jjsprandel/SCAN_PCB/hardware_design/exports/3d_models/full_back_zoomed.png

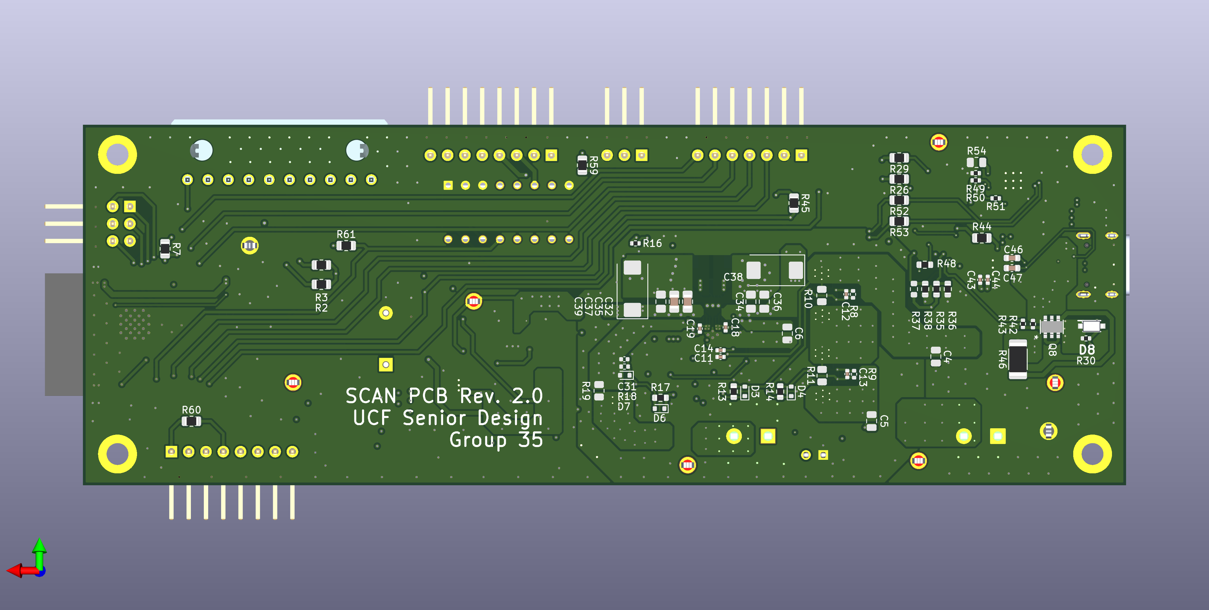
hardware_design/exports/3d_models/full_back_zoomed.png
