jjsprandel/SCAN_PCB/hardware_design/exports/3d_models/power_management.png

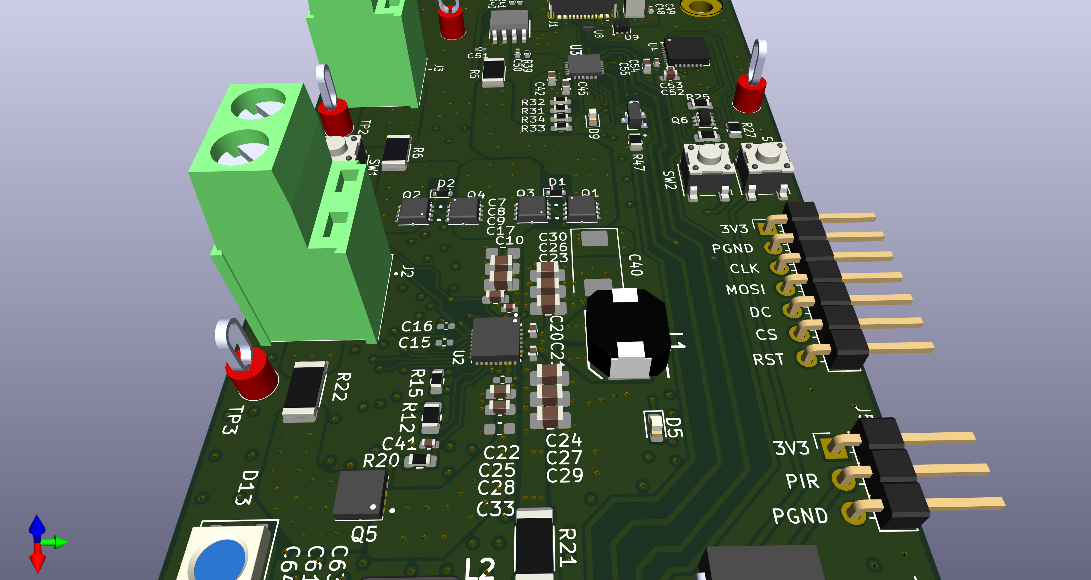
hardware_design/exports/3d_models/power_management.png
