jjsprandel/SCAN_PCB/hardware_design/exports/3d_models/regulators.png

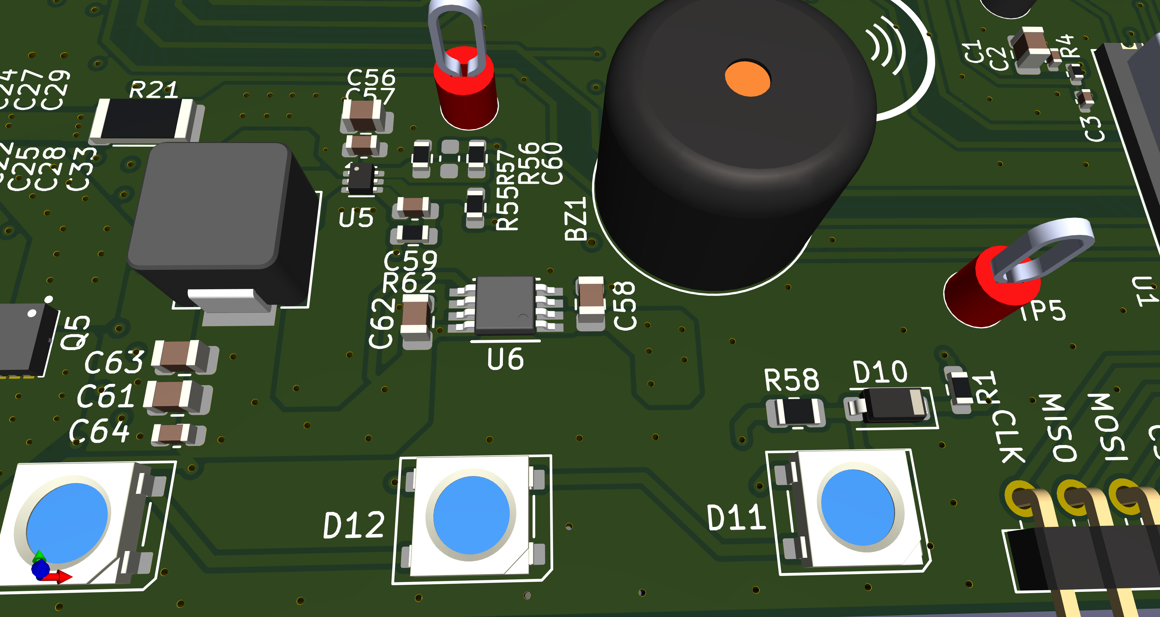
hardware_design/exports/3d_models/regulators.png
