jjsprandel/SCAN_PCB/hardware_design/exports/3d_models/side_1.png

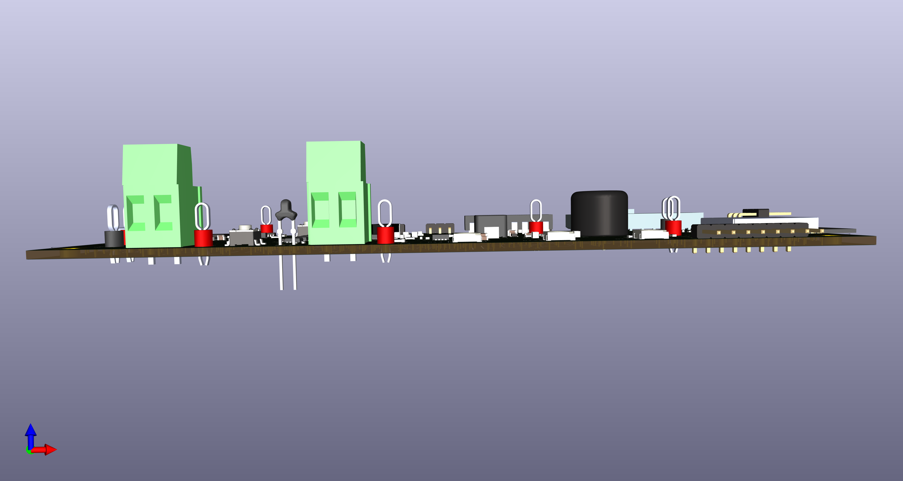
hardware_design/exports/3d_models/side_1.png
