jjsprandel/SCAN_PCB/hardware_design/exports/3d_models/USB_PD.png

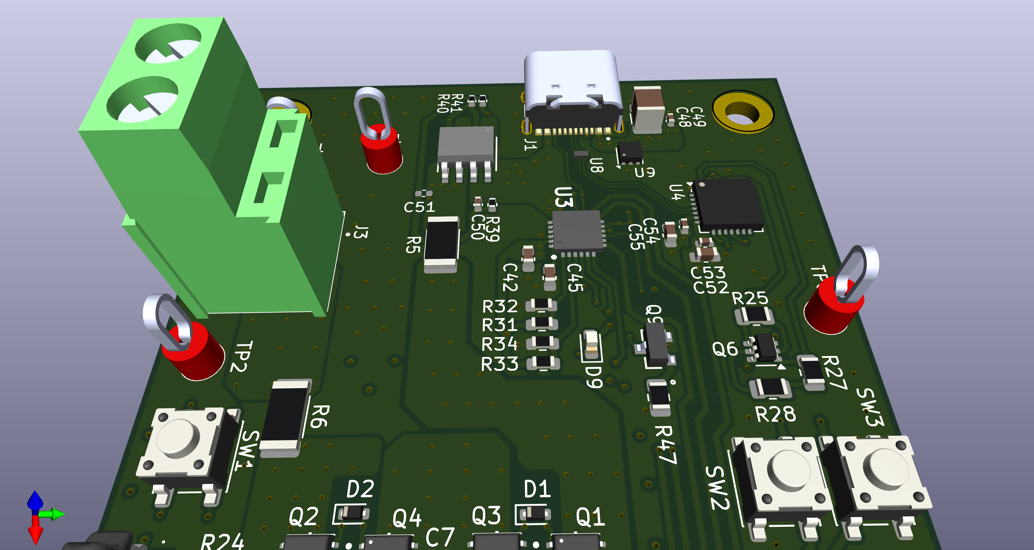
hardware_design/exports/3d_models/USB_PD.png
