jjsprandel/SCAN_PCB/hardware_design/exports/layout/multi-layer/top_gnd1.pdf

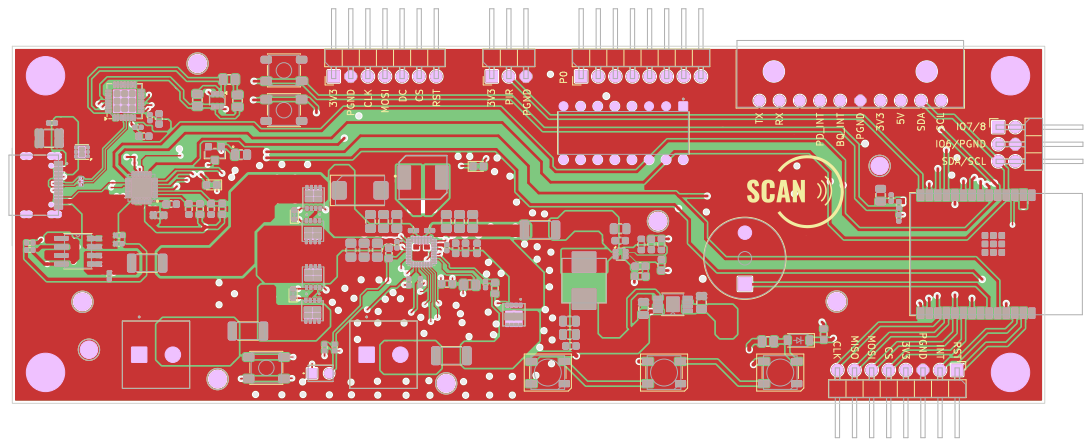
[picture p36: page 1]
