jjsprandel/SCAN_PCB/hardware_design/exports/layout/single_layer/SCAN-B_Adhesive.pdf

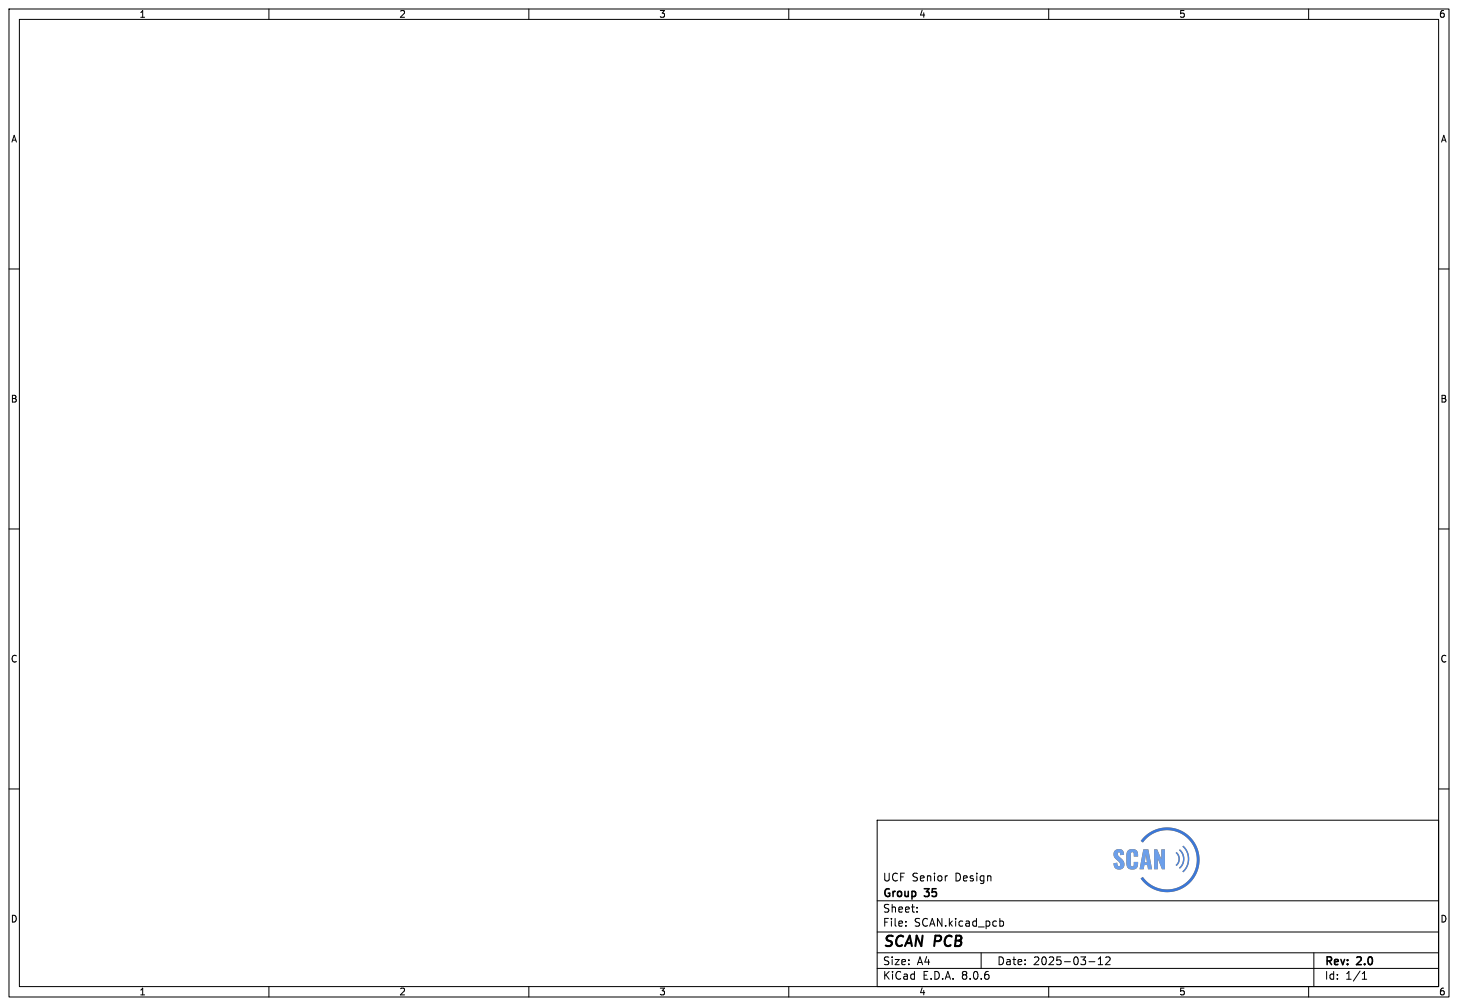
[picture p37: page 1]
