jjsprandel/SCAN_PCB/hardware_design/exports/layout/single_layer/SCAN-B_Courtyard.pdf

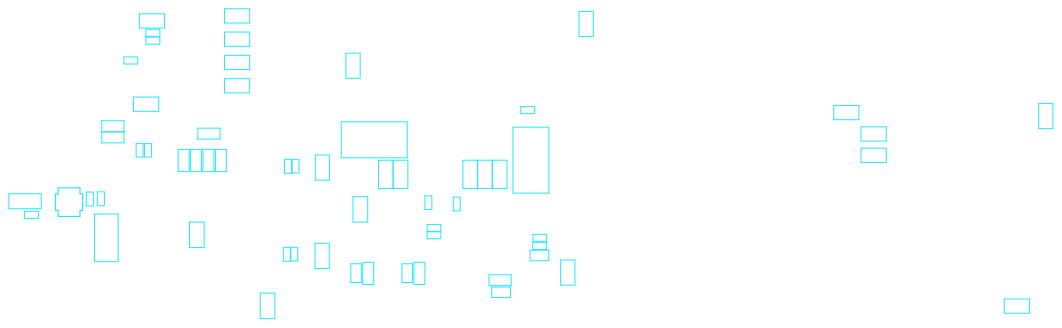
[picture p38: page 1]
