jjsprandel/SCAN_PCB/hardware_design/exports/layout/single_layer/SCAN-B_Fab.pdf

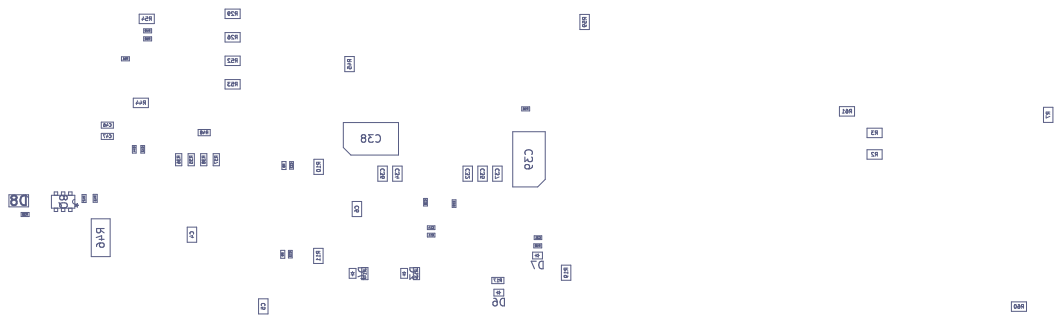
[picture p39: page 1]
