jjsprandel/SCAN_PCB/hardware_design/exports/layout/single_layer/SCAN-B_Mask.pdf

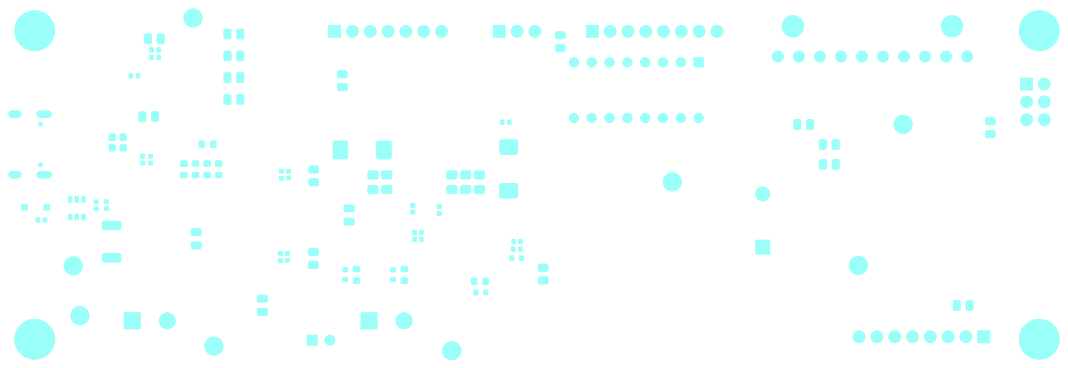
[picture p40: page 1]
