jjsprandel/SCAN_PCB/hardware_design/exports/layout/single_layer/SCAN-B_Paste.pdf

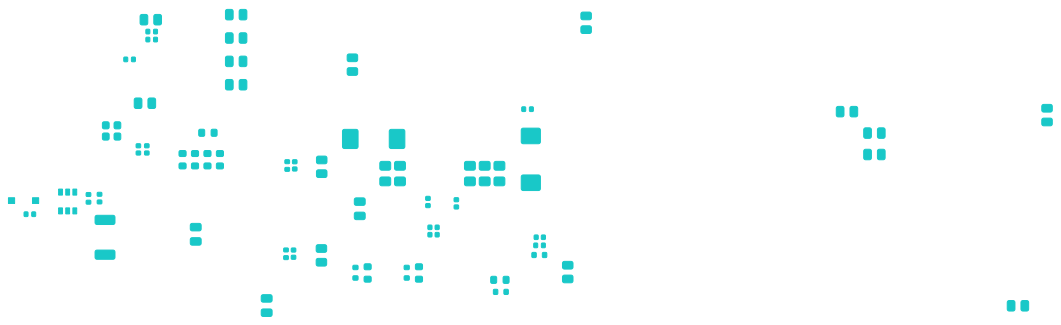
[picture p41: page 1]
