jjsprandel/SCAN_PCB/hardware_design/exports/layout/single_layer/SCAN-B_Silkscreen.pdf

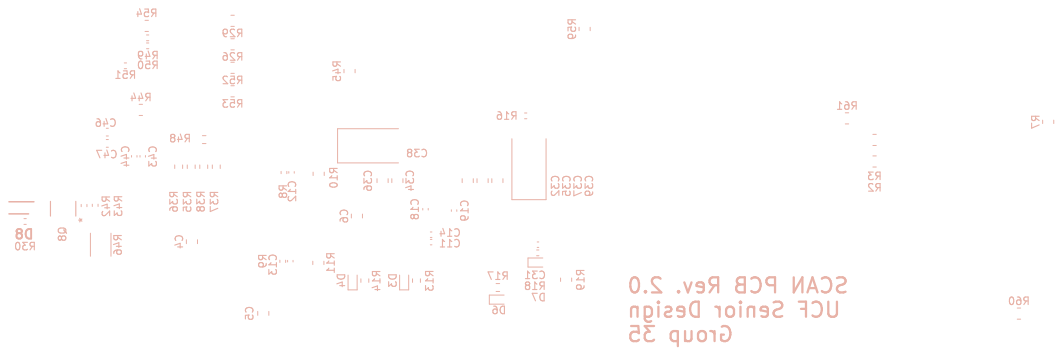
[picture p42: page 1]
