jjsprandel/SCAN_PCB/hardware_design/exports/layout/single_layer/SCAN-Bottom.pdf

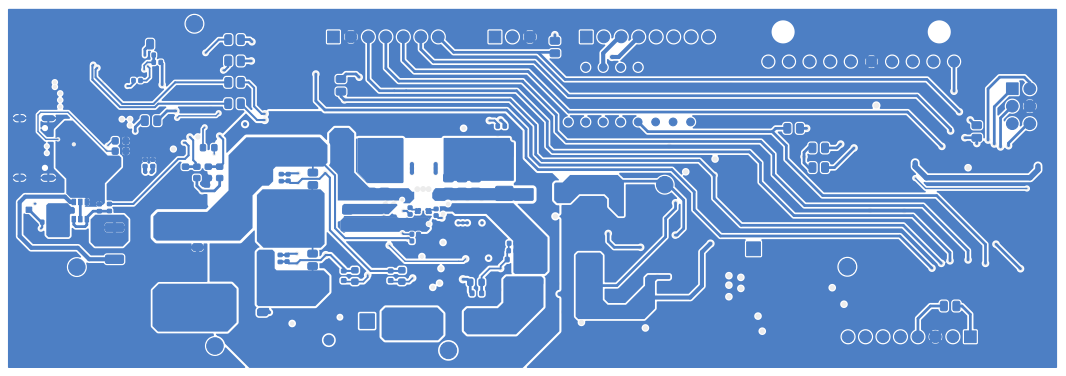
[picture p43: page 1]
