jjsprandel/SCAN_PCB/hardware_design/exports/layout/single_layer/SCAN-Edge_Cuts.pdf

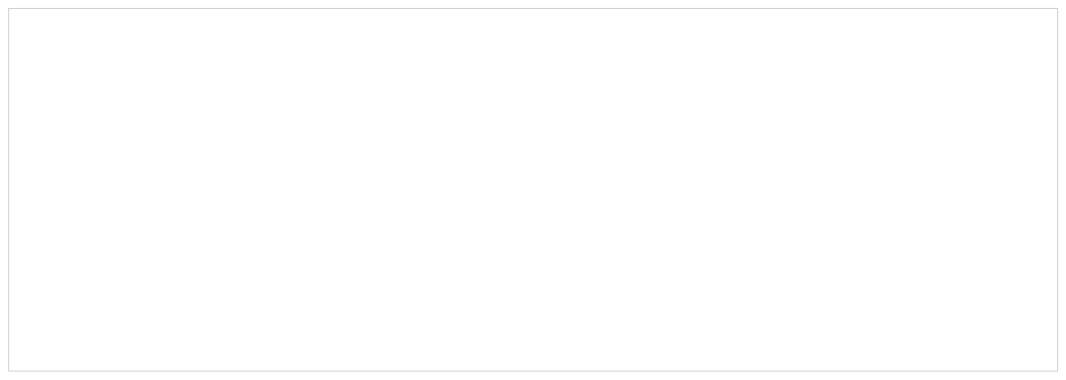
[picture p44: page 1]
