jjsprandel/SCAN_PCB/hardware_design/exports/layout/single_layer/SCAN-F_Courtyard.pdf

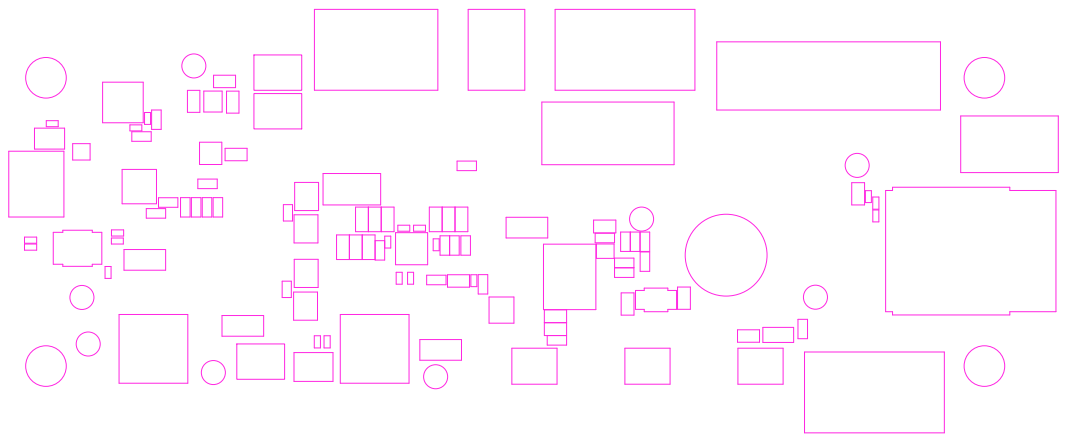
[picture p45: page 1]
