jjsprandel/SCAN_PCB/hardware_design/exports/layout/single_layer/SCAN-F_Fab.pdf

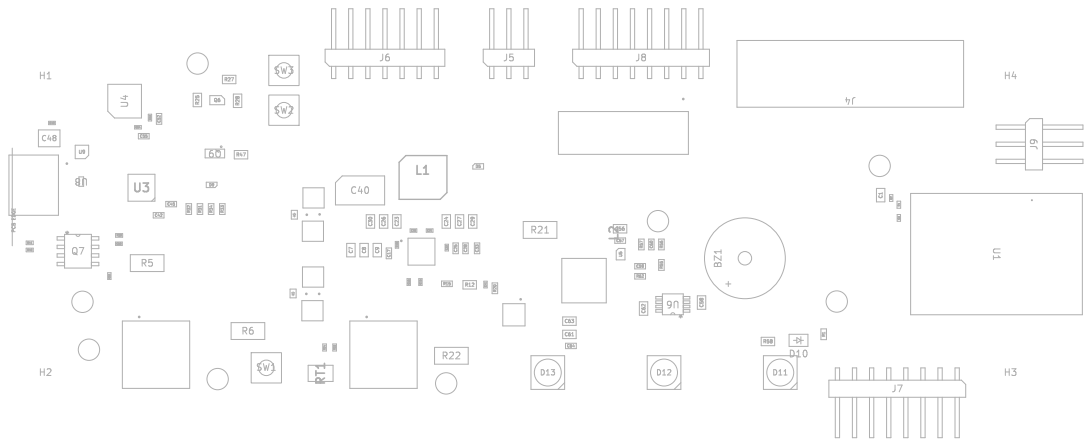
[picture p46: page 1]
