jjsprandel/SCAN_PCB/hardware_design/exports/layout/single_layer/SCAN-F_Mask.pdf

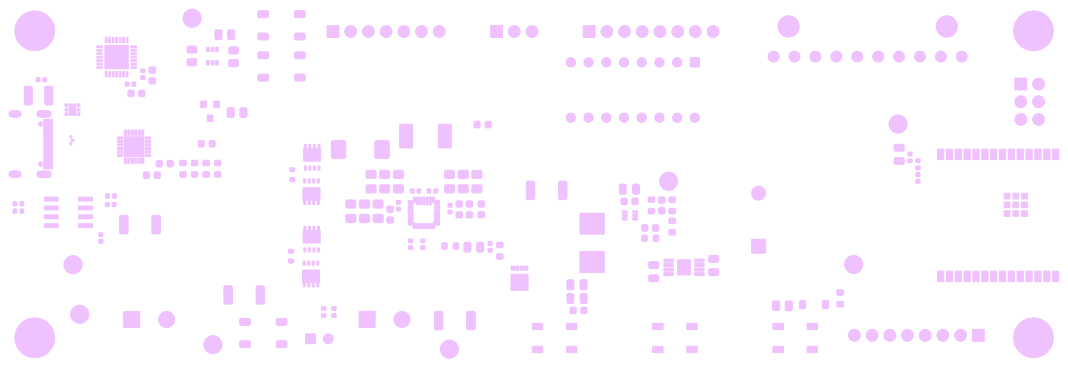
[picture p47: page 1]
