jjsprandel/SCAN_PCB/hardware_design/exports/layout/single_layer/SCAN-F_Paste.pdf

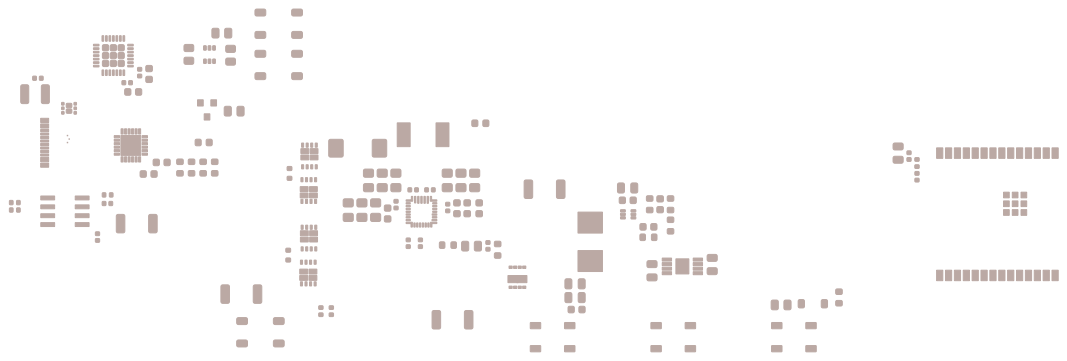
[picture p48: page 1]
