jjsprandel/SCAN_PCB/hardware_design/exports/layout/single_layer/SCAN-F_Silkscreen.pdf

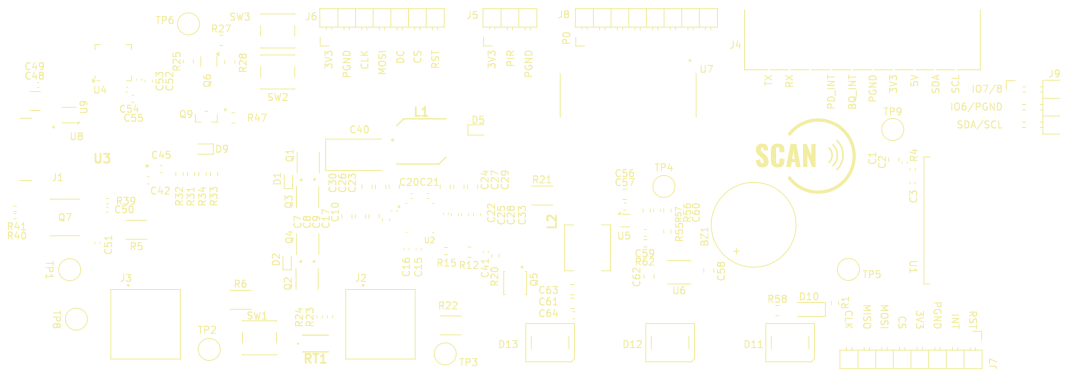
[picture p49: page 1]
