jjsprandel/SCAN_PCB/hardware_design/exports/layout/single_layer/SCAN-GND1.pdf

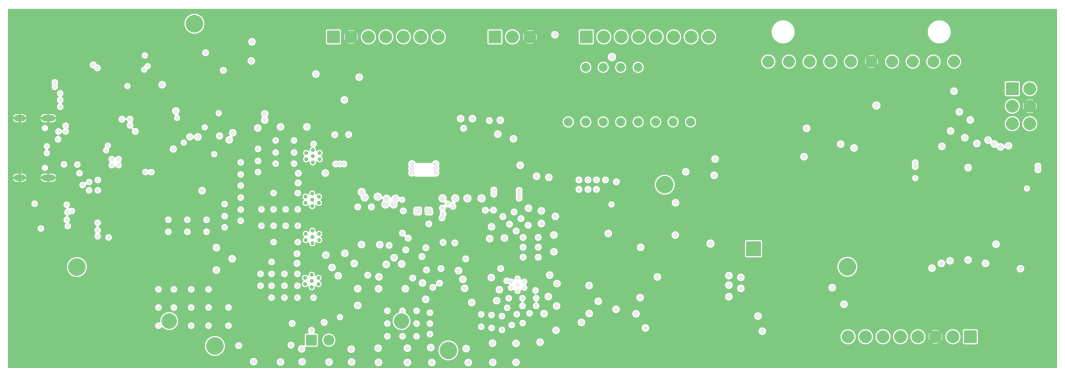
[picture p50: page 1]
