jjsprandel/SCAN_PCB/hardware_design/exports/layout/single_layer/SCAN-GND2.pdf

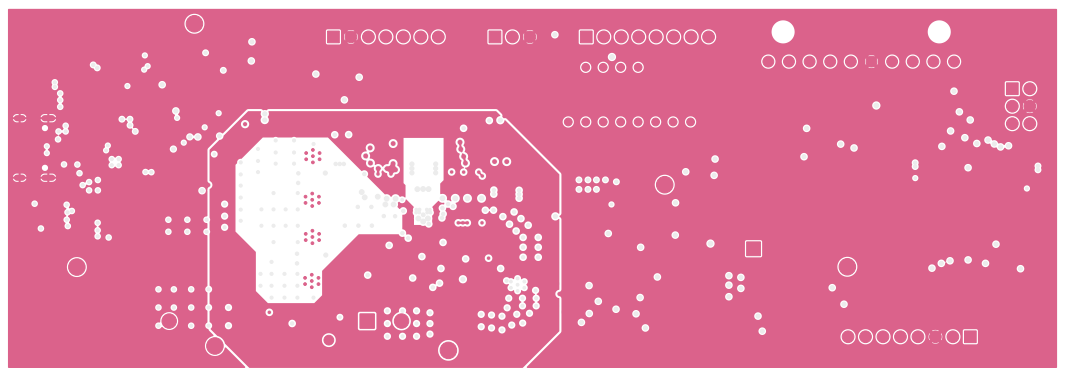
[picture p51: page 1]
