jjsprandel/SCAN_PCB/hardware_design/exports/layout/single_layer/SCAN-PCB_Mounting.pdf

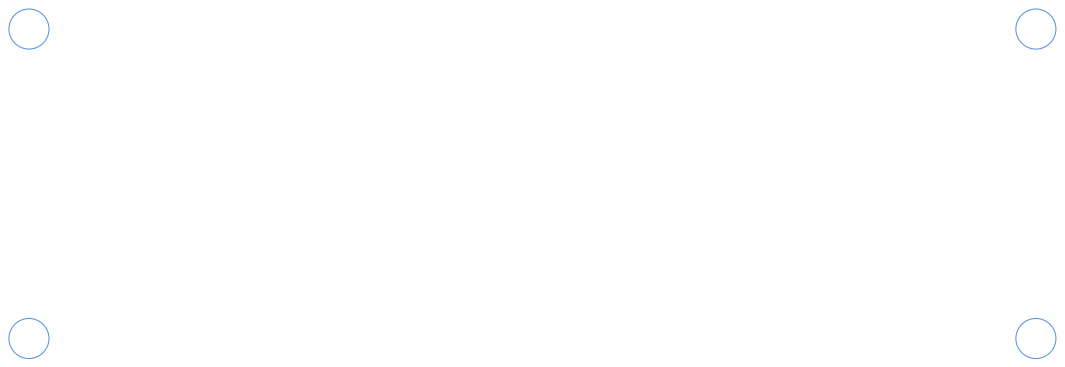
[picture p52: page 1]
