jjsprandel/SCAN_PCB/hardware_design/exports/layout/single_layer/SCAN-PWR.pdf

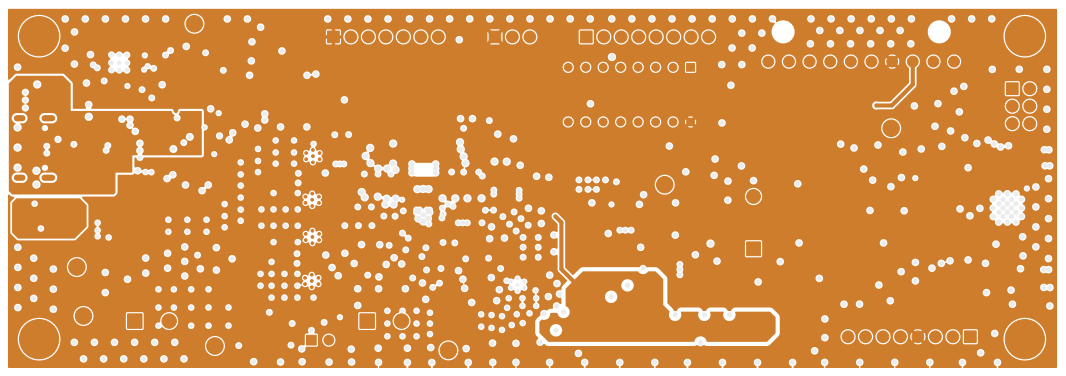
[picture p53: page 1]
