jjsprandel/SCAN_PCB/hardware_design/exports/layout/single_layer/SCAN-SIG.pdf

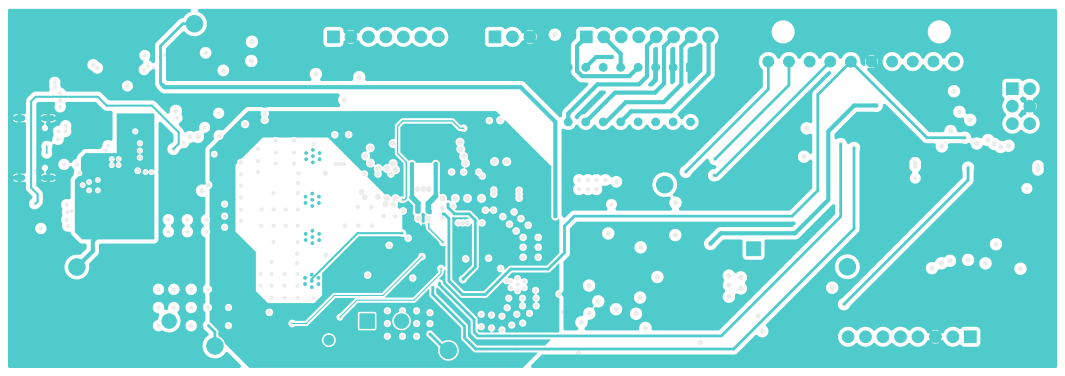
[picture p54: page 1]
