jjsprandel/SCAN_PCB/hardware_design/exports/layout/single_layer/SCAN-Top.pdf

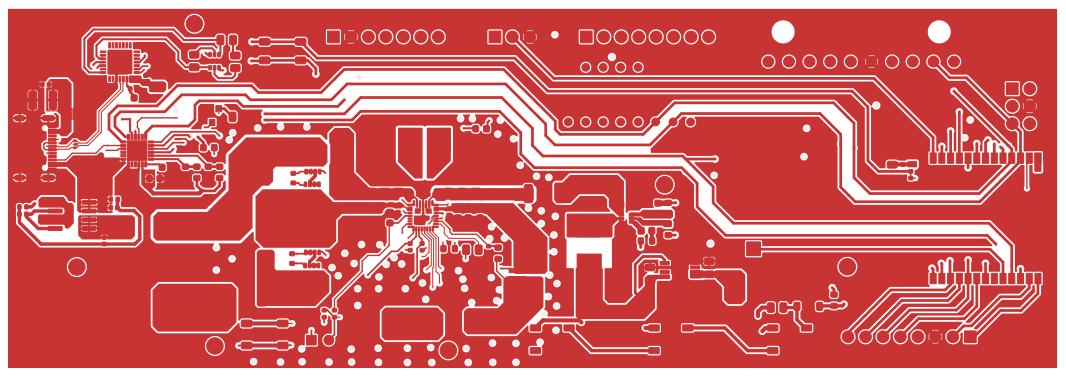
[picture p55: page 1]
