jjsprandel/SCAN_PCB/hardware_design/exports/layout/single_layer/SCAN-User_Eco2.pdf

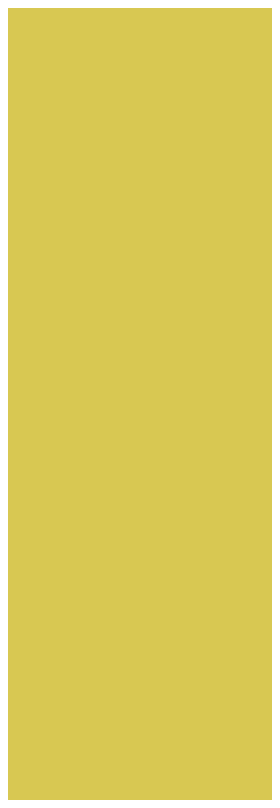
[picture p56: page 1]
